nanocastro/Medidor-de-CO2/Imagenes/WhatsApp Image 2021-03-15 at 12.08.56 (1).jpeg

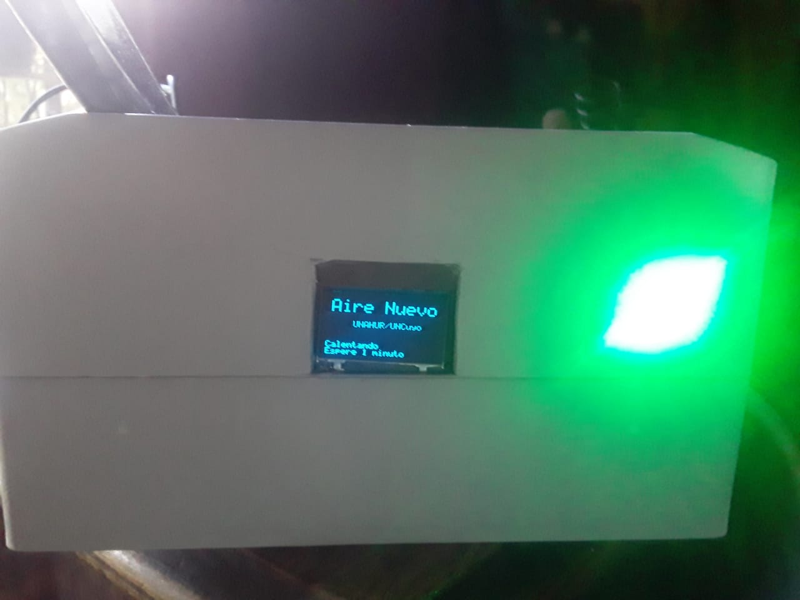
Imagenes/WhatsApp Image 2021-03-15 at 12.08.56 (1).jpeg
